microcontrollersig/brian-led-matrix-petrol-signs/B.png

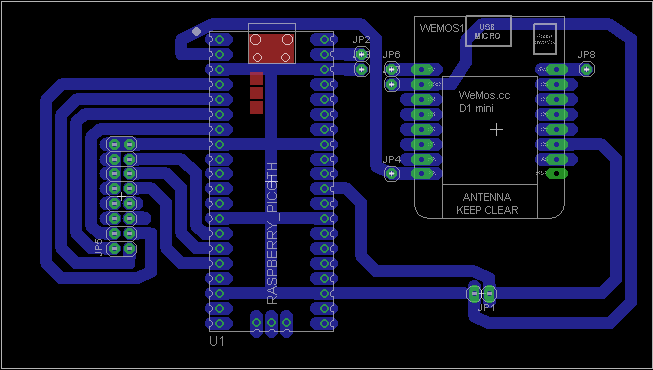
B.png
