microcontrollersig/brian-led-matrix-petrol-signs/C.png

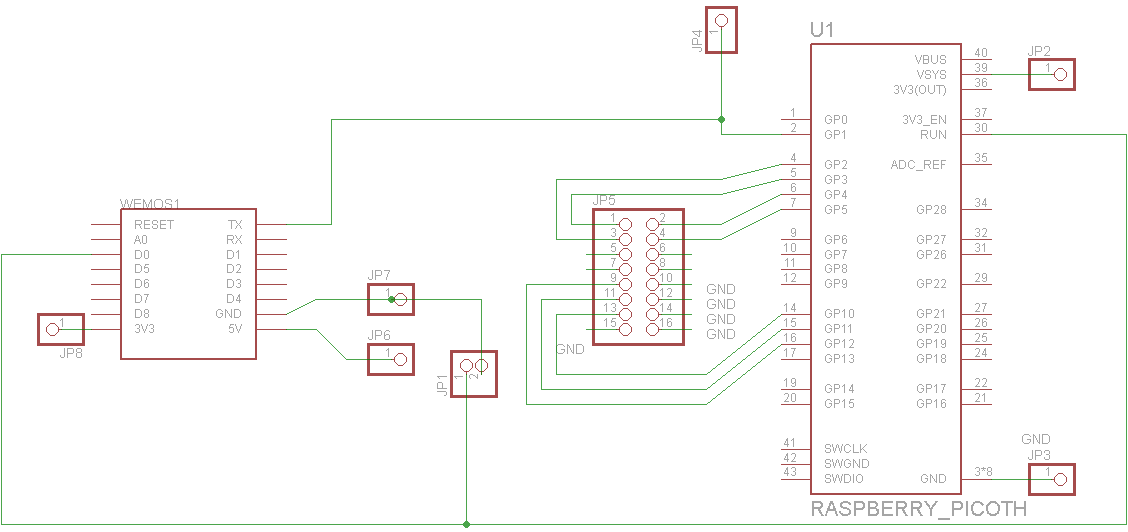
C.png
