microcontrollersig/brian-led-matrix-petrol-signs/cat4016fbd.jpg

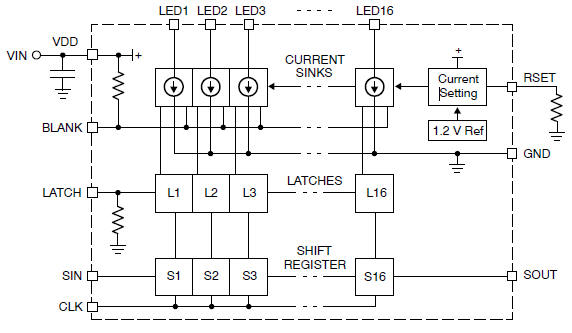
cat4016fbd.jpg
