microcontrollersig/brian-led-matrix-petrol-signs/code/d1mini/pbm/24by8mazegenerator.png

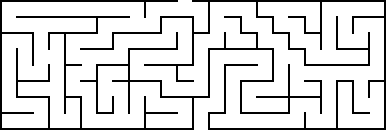
code/d1mini/pbm/24by8mazegenerator.png
