microcontrollersig/brian-led-matrix-petrol-signs/code/d1mini/pbm/thickmaze.png

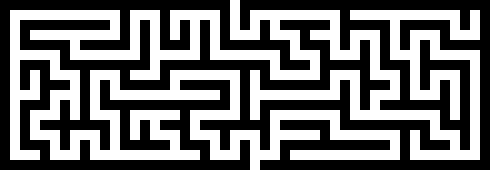
code/d1mini/pbm/thickmaze.png
