microcontrollersig/brian-led-matrix-petrol-signs/D.png

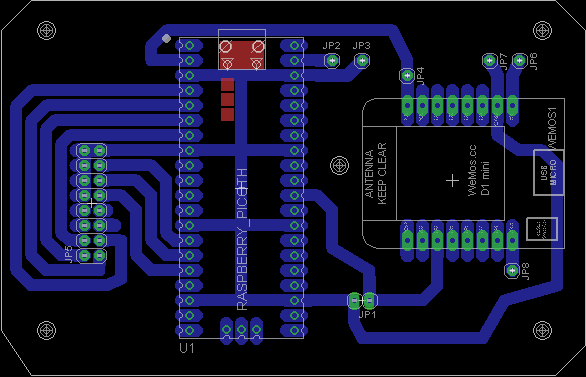
D.png
