microcontrollersig/brian-led-matrix-petrol-signs/eagle/brianPCB-bottom.png

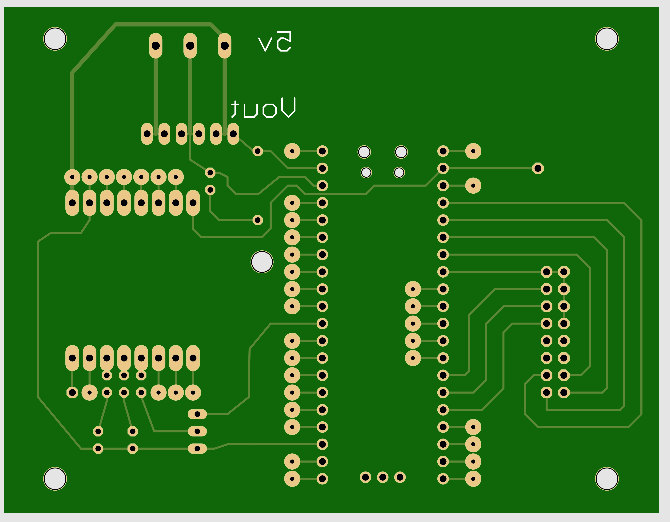
eagle/brianPCB-bottom.png
