microcontrollersig/brian-led-matrix-petrol-signs/eagle/brianPCB-top.png

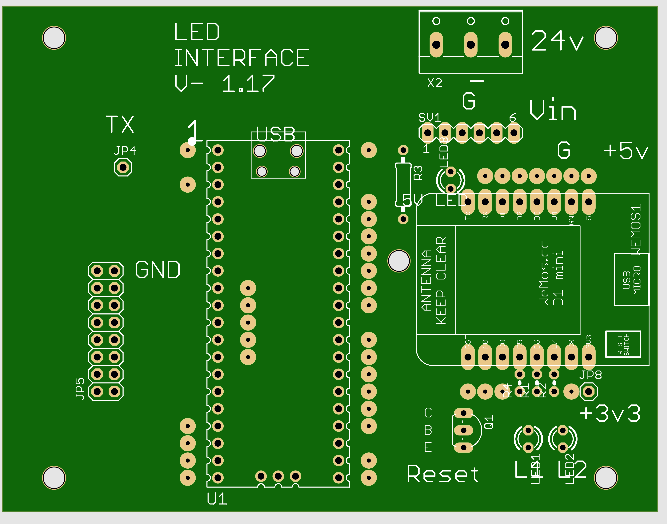
eagle/brianPCB-top.png
