microcontrollersig/brian-led-matrix-petrol-signs/eagle/Brians board 5.jpg

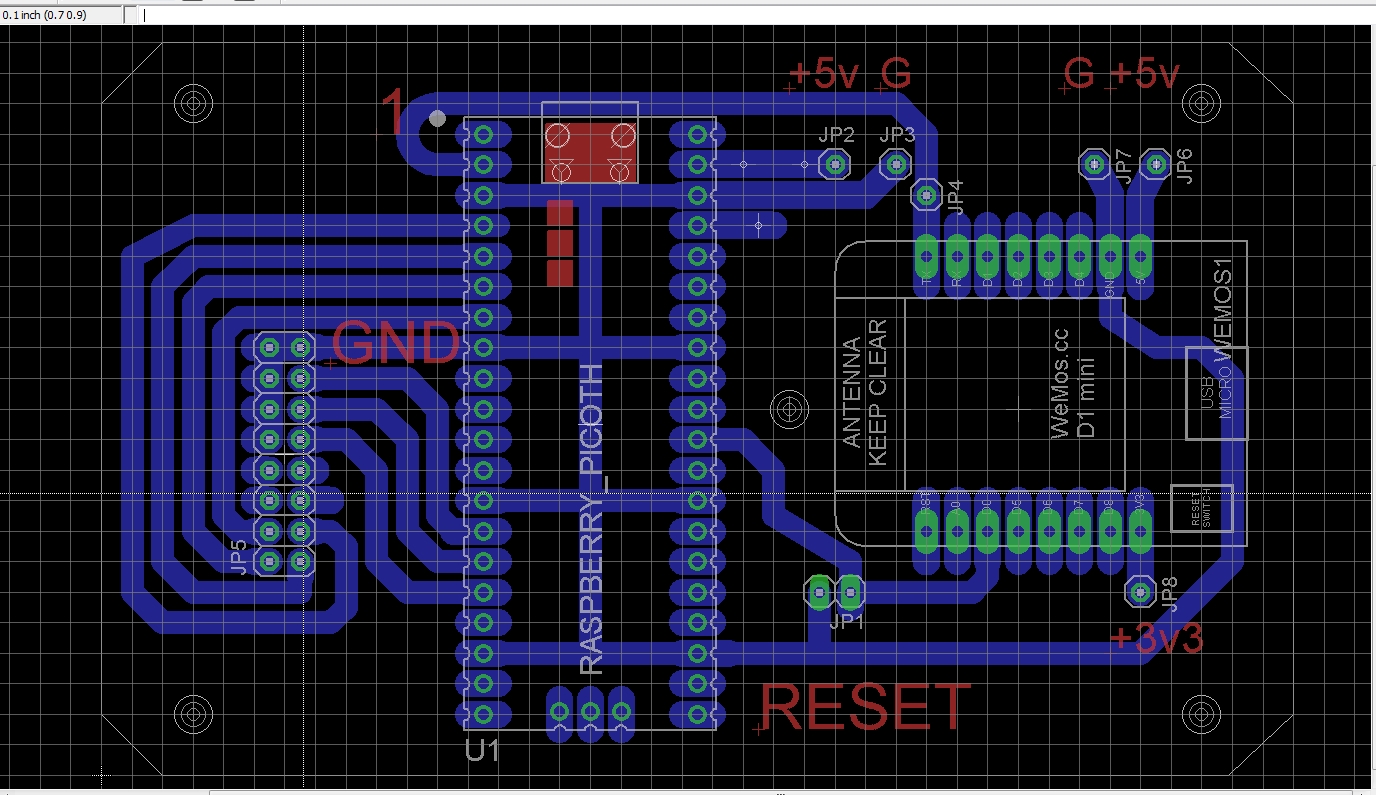
eagle/Brians board 5.jpg
