microcontrollersig/brian-led-matrix-petrol-signs/eagle/Brians board 7.jpg

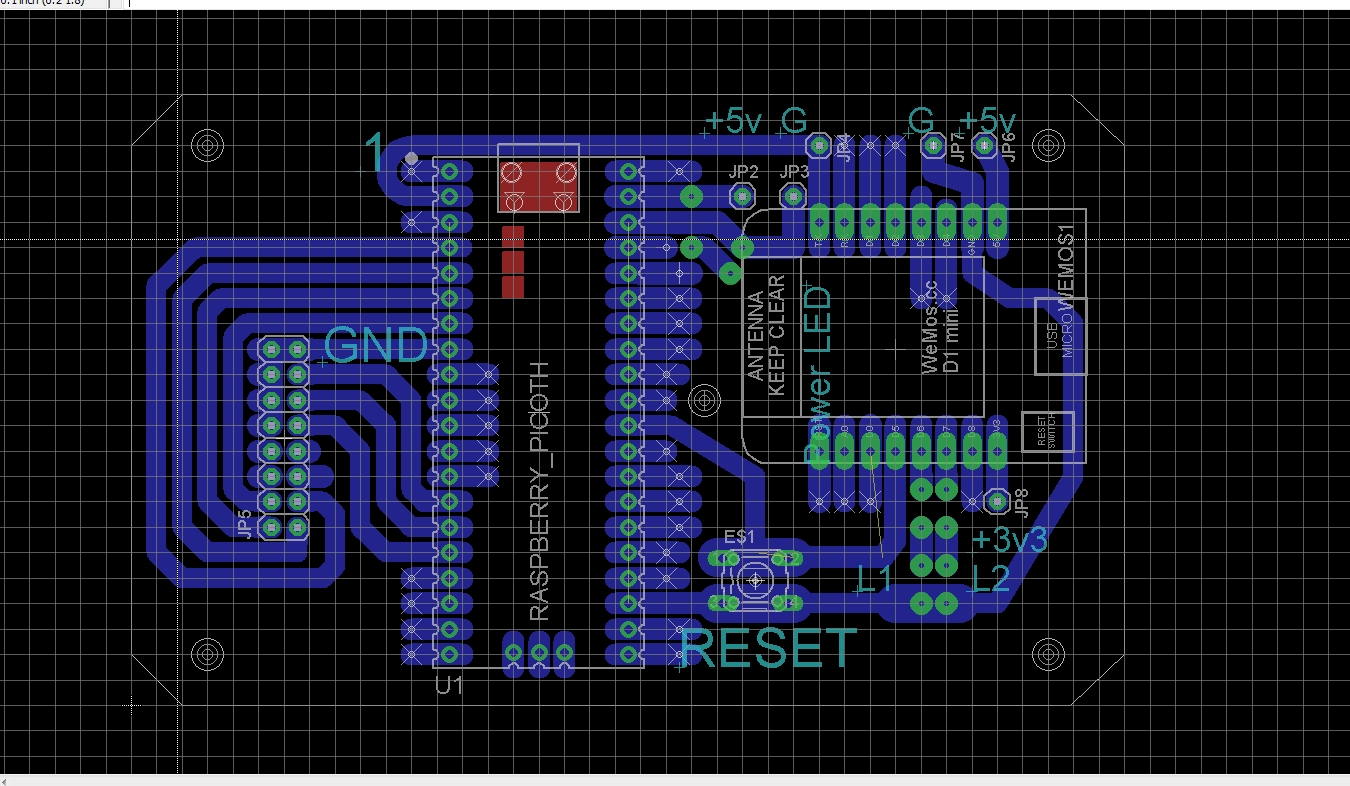
eagle/Brians board 7.jpg
