microcontrollersig/brian-led-matrix-petrol-signs/eagle/Brians LED Brd6..jpg

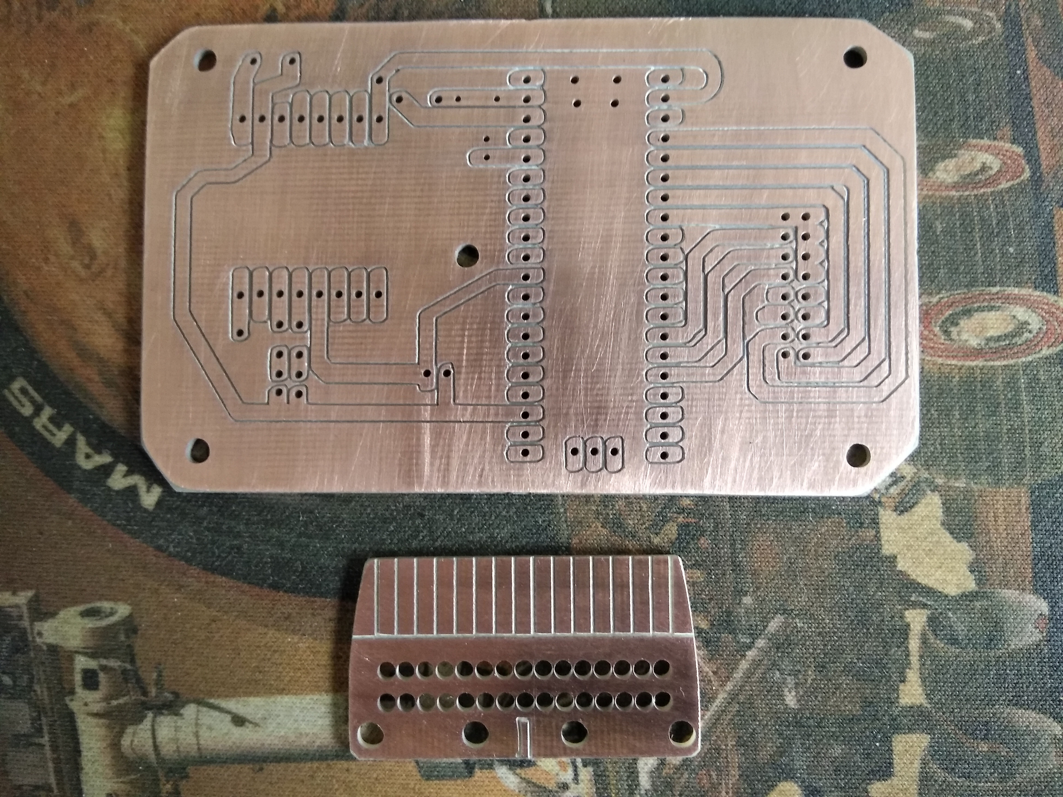
eagle/Brians LED Brd6..jpg
