microcontrollersig/brian-led-matrix-petrol-signs/eagle/Brians LED Brd6Top..jpg

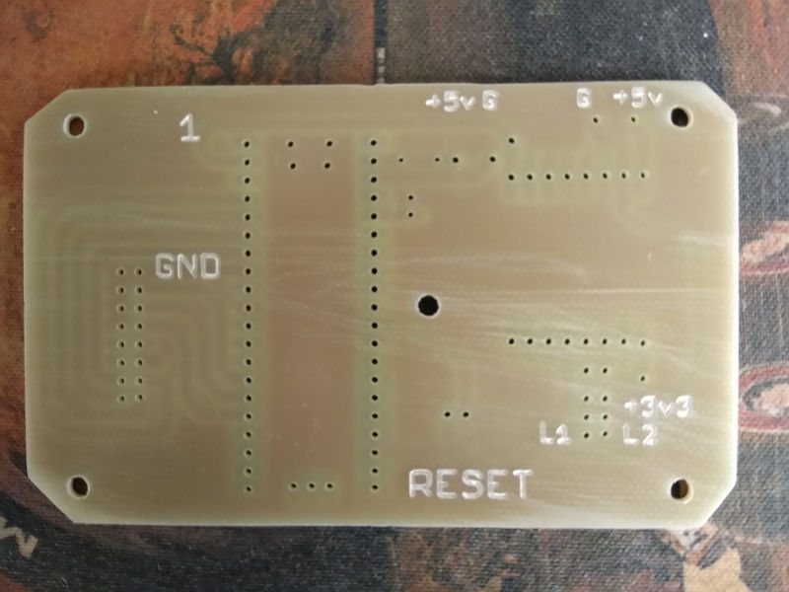
eagle/Brians LED Brd6Top..jpg
