microcontrollersig/brian-led-matrix-petrol-signs/eagle/Brians Schema 5.jpg

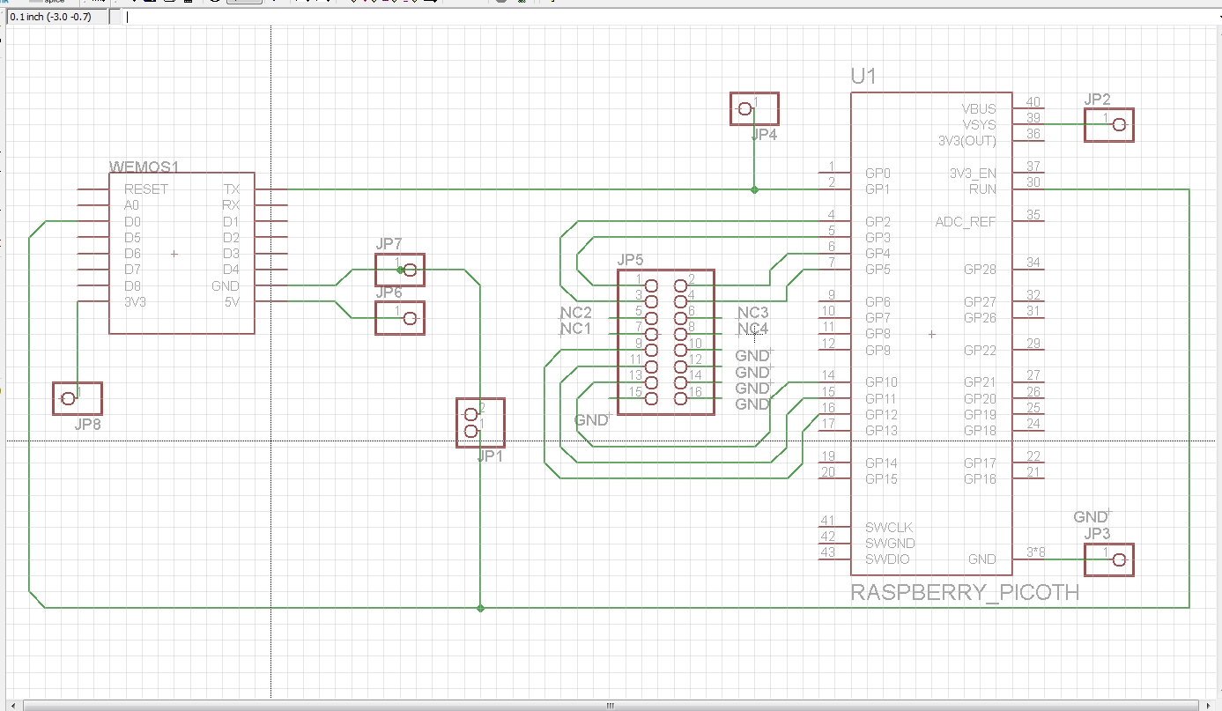
eagle/Brians Schema 5.jpg
