microcontrollersig/brian-led-matrix-petrol-signs/eagle/jlcpcb-12-bottom.png

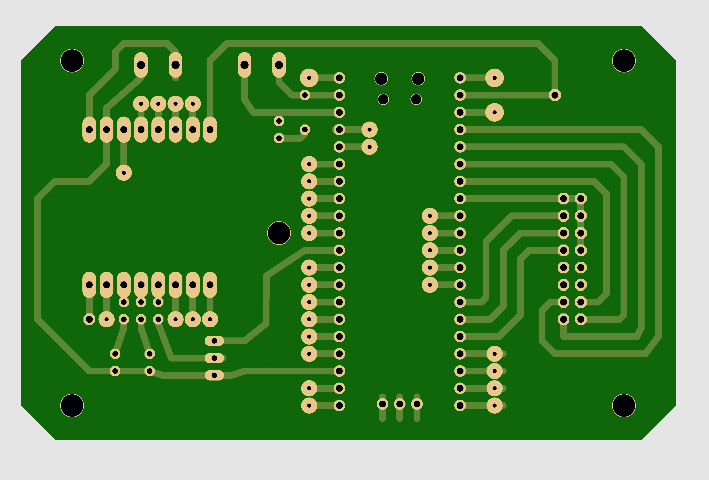
eagle/jlcpcb-12-bottom.png
