microcontrollersig/brian-led-matrix-petrol-signs/eagle/jlcpcb-12-top.png

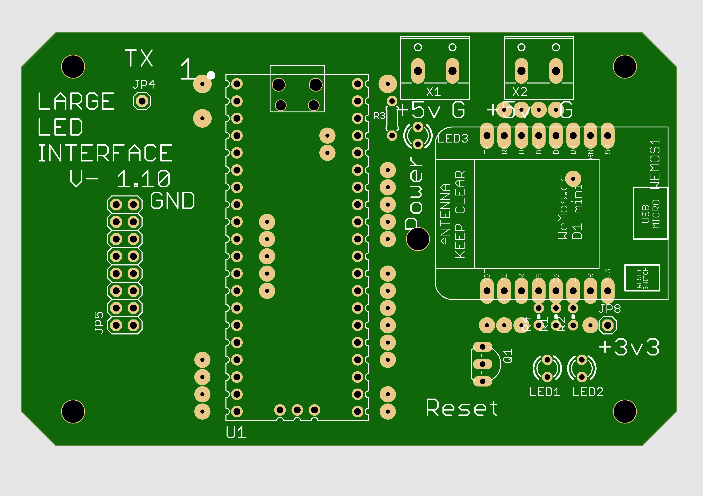
eagle/jlcpcb-12-top.png
