microcontrollersig/brian-led-matrix-petrol-signs/images/20210626_175617.jpg

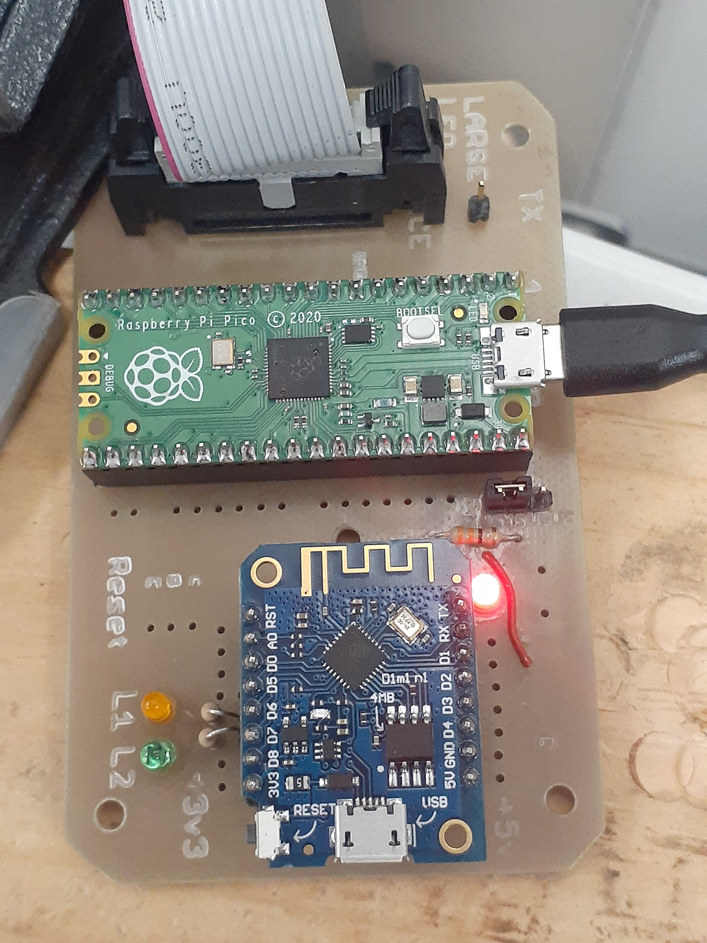
images/20210626_175617.jpg
