microcontrollersig/brian-led-matrix-petrol-signs/images/20210626_175921.jpg

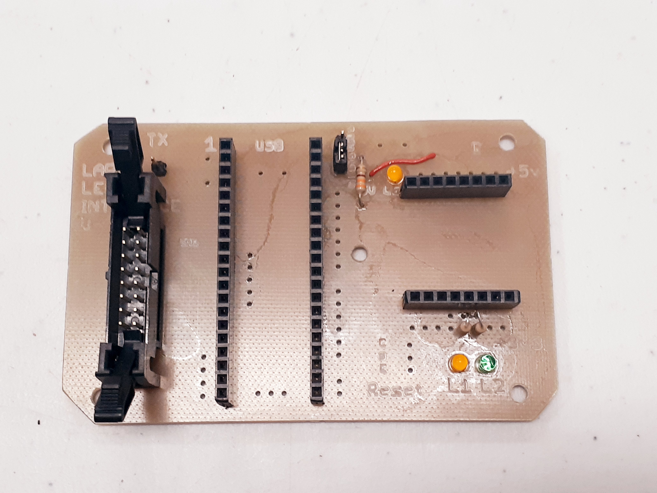
images/20210626_175921.jpg
