microcontrollersig/brian-led-matrix-petrol-signs/images/buckconverter.png

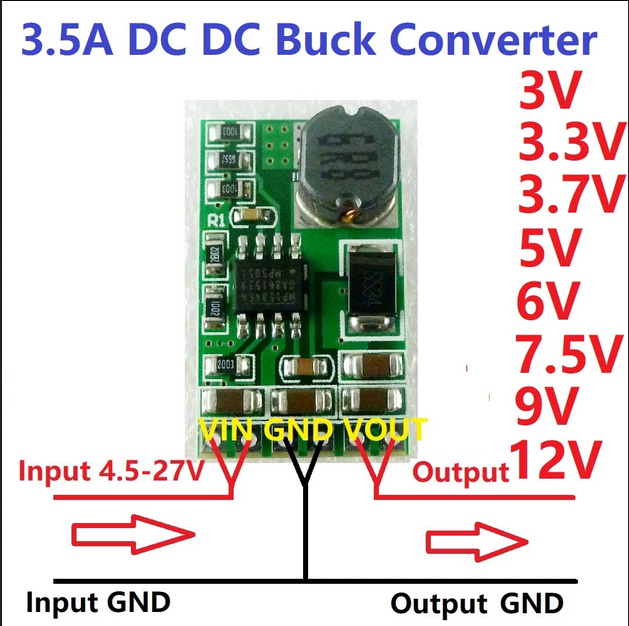
images/buckconverter.png
