microcontrollersig/brian-led-matrix-petrol-signs/images/esphomeflasher.jpg

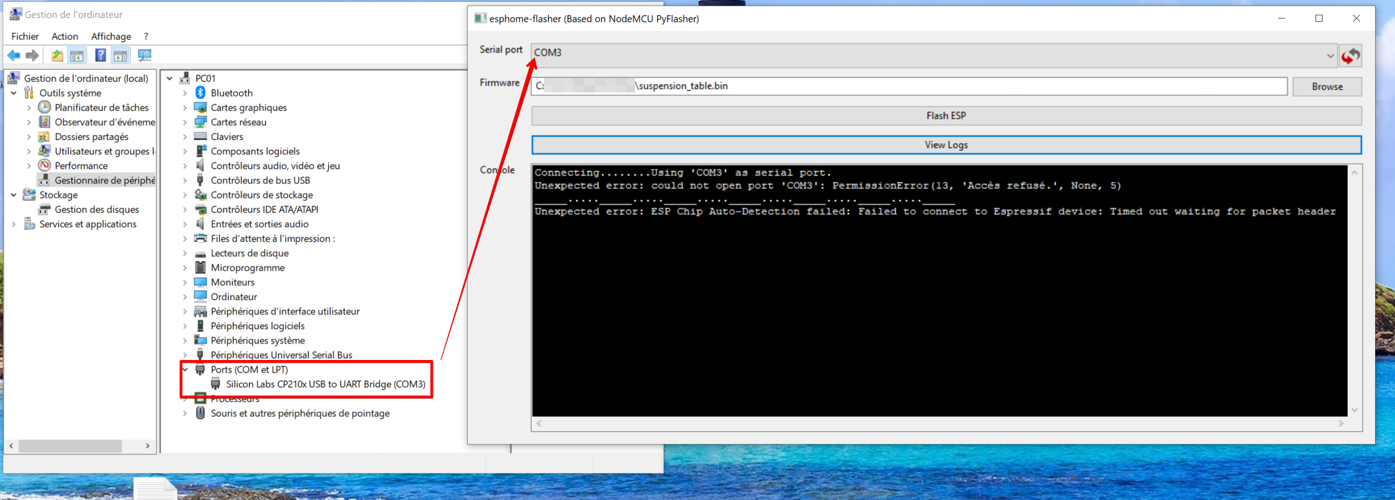
images/esphomeflasher.jpg
