microcontrollersig/brian-led-matrix-petrol-signs/LED-control-system-conversion-card-HUB08-connection-board-adapter-with-8-hub08-port-included.jpg_Q90.jpg_.jpg

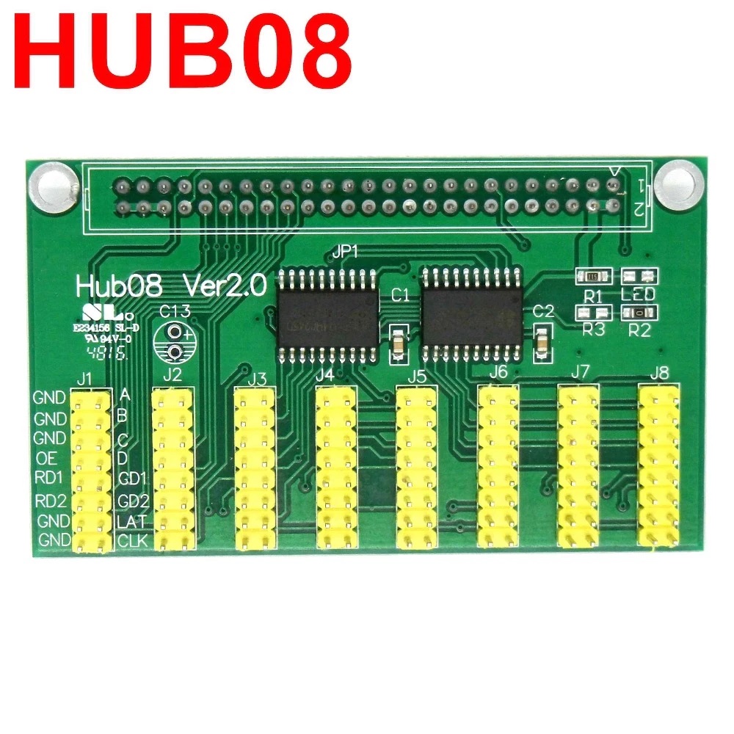
LED-control-system-conversion-card-HUB08-connection-board-adapter-with-8-hub08-port-included.jpg_Q90.jpg_.jpg
