microcontrollersig/brian-led-matrix-petrol-signs/eagle/Brians test board 1.12a-topPCB-mohan.png

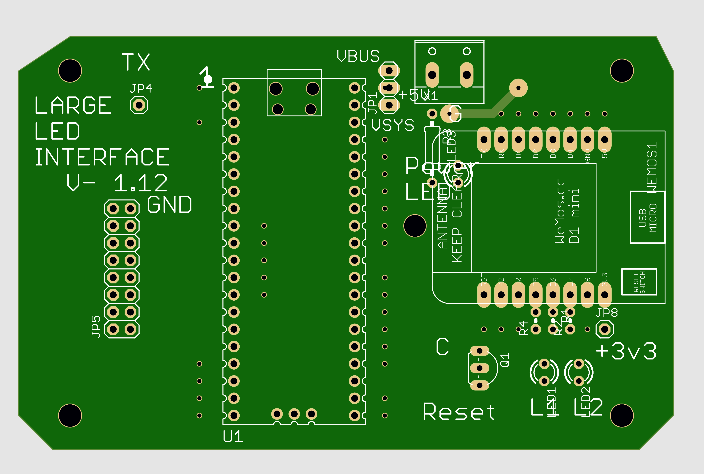
eagle/Brians test board 1.12a-topPCB-mohan.png
