microcontrollersig/brian-led-matrix-petrol-signs/eagle/Brians test board 12.png

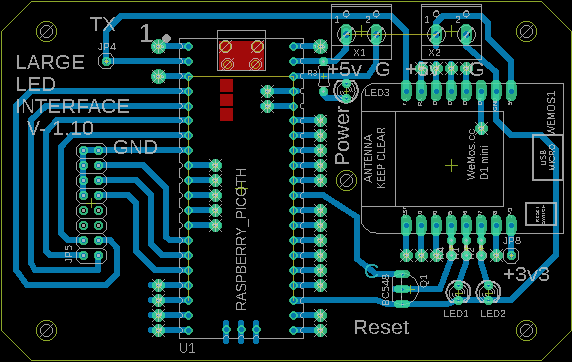
eagle/Brians test board 12.png
