microcontrollersig/brian-led-matrix-petrol-signs/eagle/Brians test board 16-board.png

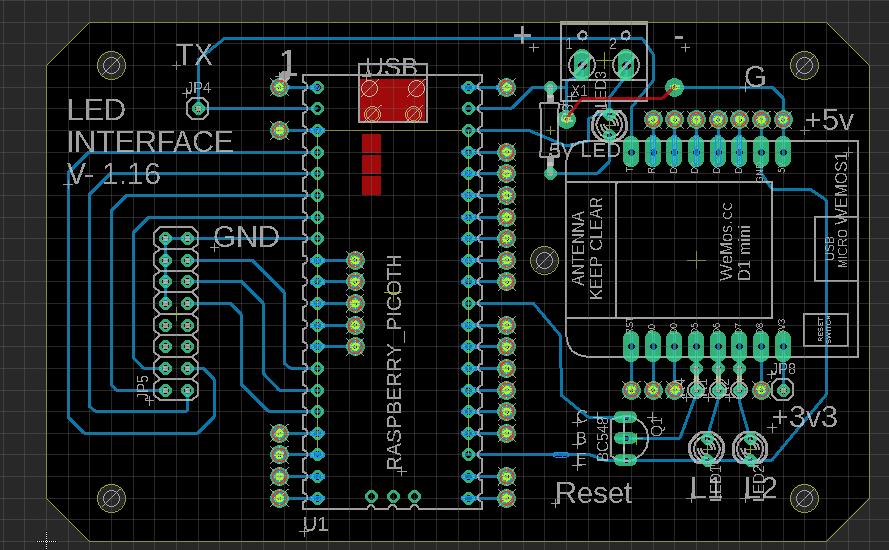
eagle/Brians test board 16-board.png
