microcontrollersig/brian-led-matrix-petrol-signs/eagle/Brians test board 16-bottom.png

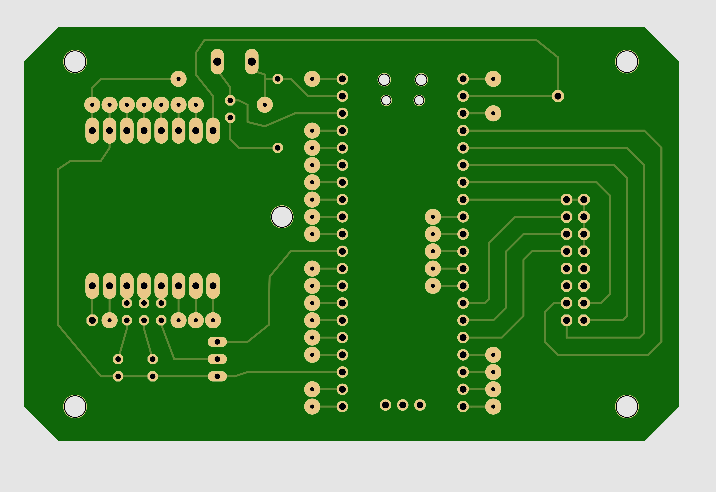
eagle/Brians test board 16-bottom.png
