microcontrollersig/brian-led-matrix-petrol-signs/eagle/Brians test board 16-top.png

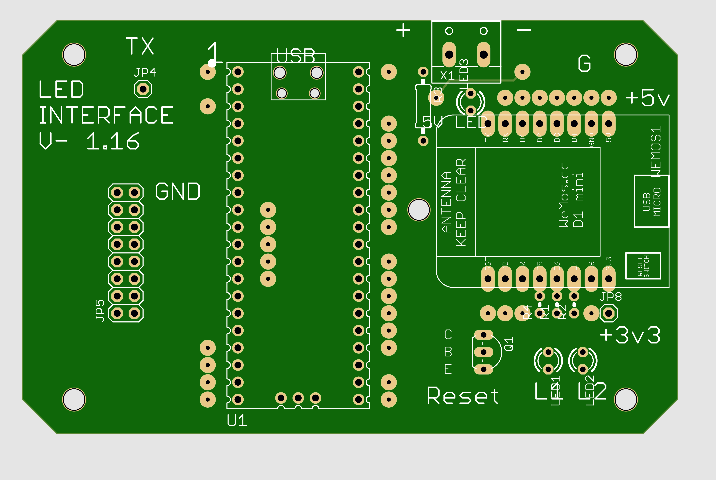
eagle/Brians test board 16-top.png
