microcontrollersig/brian-led-matrix-petrol-signs/code/012-multipaneldemos/012-multipaneldemos.ino

#include "dispatcher.h"
#include "DMD3.h"
#include "customglcdfonts.h"

#if defined(ARDUINO_ARCH_RP2040)
#define PIN_DATA1 6 
#define PIN_DATA2 7
#define PIN_DATA3 8
#define PIN_DATA4 9

#define PIN_CLK 2
#define PIN_LATCH 3 
#define PIN_NOE 4
#elif defined(ESP8266)
#define PIN_DATA1 D6
#define PIN_DATA2 D2
#define PIN_DATA3 D1
#define PIN_DATA4 D8

#define PIN_CLK D7
#define PIN_LATCH D0
#define PIN_NOE D5
#endif
// TX = 0 
// RX = 1

#define PANELS_WIDTH 6
#define PANELS_HEIGHT 2

DMD3 display(PANELS_WIDTH, PANELS_HEIGHT);

Dispatcher *runner;

void setup() {
  Serial.begin(115200);
  delay(5000);

  display.begin(PIN_CLK, PIN_LATCH, PIN_NOE, PIN_DATA1, PIN_DATA2, PIN_DATA3, PIN_DATA4);
  display.setBrightness(0.1);
  display.setFont(ArialFont16x16);
  
  runner = new Dispatcher(&display);
  //runner->dispatch('0');
}

void loop() {
  runner->handleSerialInput();
  //delay(5000);
}
