microcontrollersig/brian-led-matrix-petrol-signs/code/dmd3v2/Droid_Sans_24.h

static const uint8_t Droid_Sans_24[] PROGMEM = {
    0x5C, 0xE1, // size
    0x0A, // width
    0x19, // height
    0x20, // first char
    0x60, // char count
    
    // char widths
    0x00, 0x03, 0x07, 0x0E, 0x0A, 0x12, 0x10, 0x02, 0x06, 0x06, 
    0x0A, 0x0B, 0x04, 0x06, 0x03, 0x09, 0x0B, 0x06, 0x0B, 0x0B, 
    0x0D, 0x0B, 0x0B, 0x0B, 0x0B, 0x0B, 0x03, 0x04, 0x0B, 0x0B, 
    0x0B, 0x09, 0x12, 0x0E, 0x0B, 0x0C, 0x0C, 0x09, 0x09, 0x0E, 
    0x0C, 0x06, 0x04, 0x0C, 0x09, 0x10, 0x0D, 0x0F, 0x0A, 0x0F, 
    0x0B, 0x0A, 0x0C, 0x0C, 0x0D, 0x14, 0x0C, 0x0C, 0x0A, 0x05, 
    0x09, 0x05, 0x0D, 0x0A, 0x05, 0x0A, 0x0B, 0x09, 0x0B, 0x0B, 
    0x07, 0x0C, 0x0A, 0x02, 0x04, 0x0A, 0x02, 0x12, 0x0A, 0x0C, 
    0x0B, 0x0B, 0x08, 0x09, 0x08, 0x0A, 0x0C, 0x12, 0x0C, 0x0C, 
    0x09, 0x07, 0x02, 0x07, 0x0B, 0x0A, 
    
    // font data
    0xFC, 0xFC, 0xFC, 0x07, 0x3F, 0x00, 0x07, 0x07, 0x07, 0x00, 0x00, 0x00, // 33
    0xFC, 0xFC, 0x00, 0x00, 0x00, 0xFC, 0xFC, 0x00, 0x00, 0x00, 0x00, 0x00, 0x00, 0x00, 0x00, 0x00, 0x00, 0x00, 0x00, 0x00, 0x00, 0x00, 0x00, 0x00, 0x00, 0x00, 0x00, 0x00, // 34
    0x00, 0x80, 0x80, 0x80, 0xE0, 0xFC, 0x84, 0x80, 0x80, 0x80, 0xFC, 0x9C, 0x80, 0x80, 0x30, 0x31, 0x31, 0xFD, 0x3F, 0x31, 0x31, 0x31, 0xF1, 0xFF, 0x37, 0x31, 0x31, 0x01, 0x00, 0x00, 0x07, 0x07, 0x00, 0x00, 0x00, 0x04, 0x07, 0x00, 0x00, 0x00, 0x00, 0x00, 0x00, 0x00, 0x00, 0x00, 0x00, 0x00, 0x00, 0x00, 0x00, 0x00, 0x00, 0x00, 0x00, 0x00, // 35
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
    
};
