microcontrollersig/brian-led-matrix-petrol-signs/code/font-cp437.h

// https://hxlvelectronicclub.github.io/dotmatrixtool/


CP437_FONT = [
    [0x00, 0x00, 0x00, 0x00, 0x00, 0x00, 0x00, 0x00],  # 0x00   NUL
    [0x7E, 0x81, 0x95, 0xB1, 0xB1, 0x95, 0x81, 0x7E],  # 0x01   ☺
    [0x7E, 0xFF, 0xEB, 0xCF, 0xCF, 0xEB, 0xFF, 0x7E],  # 0x02   ☻
    [0x0E, 0x1F, 0x3F, 0x7E, 0x3F, 0x1F, 0x0E, 0x00],  # 0x03   ♥
    [0x08, 0x1C, 0x3E, 0x7F, 0x3E, 0x1C, 0x08, 0x00],  # 0x04   ♦
    [0x18, 0xBA, 0xFF, 0xFF, 0xFF, 0xBA, 0x18, 0x00],  # 0x05   ♣
    [0x10, 0xB8, 0xFC, 0xFF, 0xFC, 0xB8, 0x10, 0x00],  # 0x06   ♠
    [0x00, 0x00, 0x18, 0x3C, 0x3C, 0x18, 0x00, 0x00],  # 0x07   •
    [0xFF, 0xFF, 0xE7, 0xC3, 0xC3, 0xE7, 0xFF, 0xFF],  # 0x08   ◘
    [0x00, 0x3C, 0x66, 0x42, 0x42, 0x66, 0x3C, 0x00],  # 0x09   ○
    [0xFF, 0xC3, 0x99, 0xBD, 0xBD, 0x99, 0xC3, 0xFF],  # 0x0A   ◙
    [0x70, 0xF8, 0x88, 0x88, 0xFD, 0x7F, 0x07, 0x0F],  # 0x0B   ♂
    [0x00, 0x4E, 0x5F, 0xF1, 0xF1, 0x5F, 0x4E, 0x00],  # 0x0C   ♀
    [0xC0, 0xE0, 0xFF, 0x7F, 0x05, 0x05, 0x07, 0x07],  # 0x0D   ♪
    [0xC0, 0xFF, 0x7F, 0x05, 0x05, 0x65, 0x7F, 0x3F],  # 0x0E   ♫
    [0x99, 0x5A, 0x3C, 0xE7, 0xE7, 0x3C, 0x5A, 0x99],  # 0x0F   ☼
    [0x7F, 0x3E, 0x3E, 0x1C, 0x1C, 0x08, 0x08, 0x00],  # 0x10   ►
    [0x08, 0x08, 0x1C, 0x1C, 0x3E, 0x3E, 0x7F, 0x00],  # 0x11   ◄
    [0x00, 0x24, 0x66, 0xFF, 0xFF, 0x66, 0x24, 0x00],  # 0x12   ↕
    [0x00, 0x5F, 0x5F, 0x00, 0x00, 0x5F, 0x5F, 0x00],  # 0x13   ‼
    [0x06, 0x0F, 0x09, 0x7F, 0x7F, 0x01, 0x7F, 0x7F],  # 0x14   ¶
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
    [0x38, 0x7C, 0x54, 0x55, 0x5D, 0x19, 0x00, 0x00],  # 0x82   é
    [0x02, 0x23, 0x75, 0x55, 0x55, 0x7D, 0x7B, 0x42],  # 0x83   â
    [0x21, 0x75, 0x54, 0x54, 0x7D, 0x79, 0x40, 0x00],  # 0x84   ä
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
    [0x00, 0x00, 0x00, 0x00, 0x00, 0x00, 0x00, 0x00],  # 0xFF   NBSP
];
