microcontrollersig/brian-led-matrix-petrol-signs/code/001-simpletest.ino

#define PIN_DATA1 A0
#define PIN_DATA2 A1
#define PIN_DATA3 A2
#define PIN_DATA4 A3

#define PIN_NOE 11
#define PIN_LATCH 10 // sometimes called strobe pin
#define PIN_CLK 9

#define SEGMENTS_PER_PANEL 4

#define DEBUG 


void fourChannelShiftOut(uint16_t data1, uint16_t data2, uint16_t data3, uint16_t data4) 
{  
    uint16_t mask = 0x8000;
  
	for (uint16_t i = 15; i >=3 ; i--)  {
        PORTC = (PORTC & 0xf0) |  (data1 & mask) >> i | (data2 & mask) >> (i-1) | (data3 & mask) >> (i-2) | (data4 & mask) >> (i-3);
        mask = mask >> 1;
		digitalWrite(PIN_CLK, HIGH);
		digitalWrite(PIN_CLK, LOW);
        #ifdef DEBUG
        Serial.print("0b");
        Serial.println(PORTC, BIN);
        delay(5000);
        #endif
	}
  
    PORTC = (PORTC & 0xf0) |  (data1 & mask) >> 2 | (data2 & mask) >> 1 | (data3 & mask) | (data4 & mask) << 1;
  	digitalWrite(PIN_CLK, HIGH);
	digitalWrite(PIN_CLK, LOW);		
    #ifdef DEBUG
          Serial.print("0b");
        Serial.println(PORTC, BIN);
        delay(5000);
    #endif
    mask = mask >> 1;
    PORTC = (PORTC & 0xf0) |  (data1 & mask) >> 1 | (data2 & mask)  | (data3 & mask) << 1 | (data4 & mask) << 2;
    digitalWrite(PIN_CLK, HIGH);
	digitalWrite(PIN_CLK, LOW);		
    #ifdef DEBUG
          Serial.print("0b");
        Serial.println(PORTC, BIN);
        delay(5000);
    #endif
    mask = mask >> 1;
    PORTC = (PORTC & 0xf0) | (data1 & mask) | (data2 & mask) << 1 | (data3 & mask) << 2 | (data4 & mask) << 3;
  	digitalWrite(PIN_CLK, HIGH);
	digitalWrite(PIN_CLK, LOW);    
    #ifdef DEBUG
          Serial.print("0b");
        Serial.println(PORTC, BIN);
        delay(5000);
    #endif
}


void setup()
{
  Serial.begin(9600);

  //sets analog pins(A0-A3) as output
  DDRC |= 0x0f;
  
  pinMode(PIN_CLK, OUTPUT);
  pinMode(PIN_LATCH, OUTPUT);
  //pinMode(PIN_NOE, OUTPUT);
  
  analogWrite(PIN_NOE, 255);
 
  
  uint16_t data1 = 0b1010101010101010;
  uint16_t data2 = 0b1110011111100111;
  uint16_t data3 = 0b0000000000000000;
  uint16_t data4 = 0b1111111111111111;

  for (int i=0; i < SEGMENTS_PER_PANEL; i++) {
    fourChannelShiftOut(data1, data2, data3, data4);  
  }
  
  digitalWrite(PIN_LATCH, HIGH);
  digitalWrite(PIN_LATCH, LOW);
  analogWrite(PIN_NOE, 255/2);


}

void loop()
{

}
