microcontrollersig/brian-led-matrix-petrol-signs/code/pico/demo-multipanel/games/dino/SmallCactus1.h

#pragma once

const  uint8_t SmallCactus1[] = {
  0x00, 0x18, 0x18, 0x99, 0x99, 0xff, 0x7e, 0x18
};
const static int SMALLCACTUS1_LENGTH = 8;
const static int SMALLCACTUS1_OFFSETX = 5;
const static int SMALLCACTUS1_OFFSETY = 19;
const static int SMALLCACTUS1_WIDTH = 8;
const static int SMALLCACTUS1_HEIGHT = 8;
