microcontrollersig/brian-led-matrix-petrol-signs/code/pico/demo-multipanel/games/dino/DinoStart.h

#pragma once

const static uint8_t DINOSTART[] = {
  0x00, 0x00, 0x00, 0x00, 0x3f, 0x00, 0x00, 0xff, 0x80, 0x00, 0xdf, 0x80,
  0x00, 0xff, 0x80, 0x00, 0xff, 0x80, 0x00, 0xff, 0x80, 0x41, 0xff, 0x80,
  0x43, 0xf0, 0x00, 0x67, 0xff, 0x00, 0x7f, 0xff, 0x00, 0x7f, 0xf0, 0x00,
  0x7f, 0xf8, 0x00, 0x3f, 0xe8, 0x00, 0x1f, 0xe0, 0x00, 0x0e, 0x80, 0x00,
  0x0c, 0x80, 0x00, 0x08, 0x80, 0x00, 0x0e, 0xe0, 0x00, 0x00, 0x00, 0x00
};
const static int DINOSTART_LENGTH = 60;
const static int DINOSTART_WIDTH = 24;
const static int DINOSTART_HEIGHT = 20;
