microcontrollersig/brian-led-matrix-petrol-signs/code/pico/demo-multipanel/customglcdfonts.h

#pragma once

#include "fonts/Verdana16x16.h"
#include "fonts/SystemFont5x7.h"
#include "fonts/spaceinvaders16x16.h"
#include <vector>

inline const std::vector<const uint8_t*> fonts = {VerdanaFont16x16, System5x7, SpaceInvadersFont16x16};
